skaman82/2.4GHz-Fatshark-Module/Documents/RX228D -90db VID only - not compatible/RX2288D.jpg

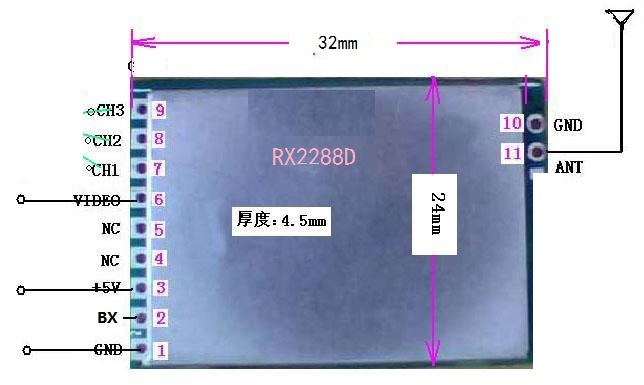
Documents/RX228D -90db VID only - not compatible/RX2288D.jpg
