skaman82/2.4GHz-Fatshark-Module/Documents/RX2189 -90db EOL no rssi/HT1ilCaFG4XXXagOFbXH.jpg

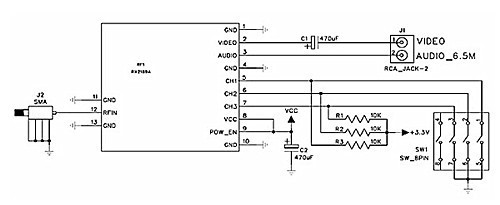
Documents/RX2189 -90db EOL no rssi/HT1ilCaFG4XXXagOFbXH.jpg
