skaman82/2.4GHz-Fatshark-Module/Documents/RX2189 -90db EOL no rssi/SKU075320.5.jpg

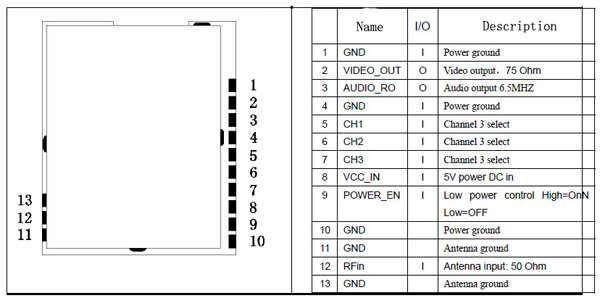
Documents/RX2189 -90db EOL no rssi/SKU075320.5.jpg
