skaman82/2.4GHz-Fatshark-Module/Documents/SM186R -90db no rssi/s-l1600-1.jpg

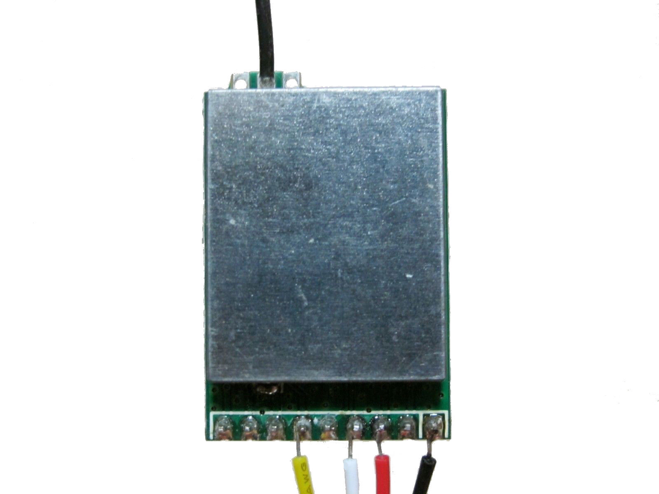
Documents/SM186R -90db no rssi/s-l1600-1.jpg
