skaman82/2.4GHz-Fatshark-Module/Documents/SM186R -90db no rssi/T2c0XlXnVNXXXXXXXX_!!104758930.jpg

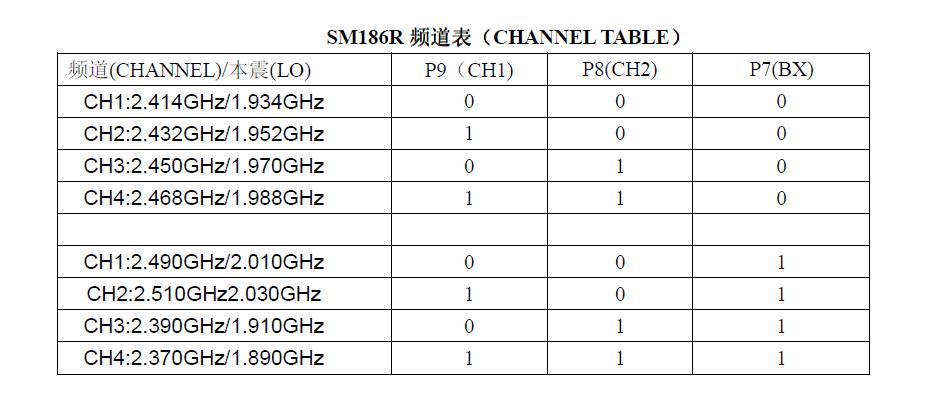
Documents/SM186R -90db no rssi/T2c0XlXnVNXXXXXXXX_!!104758930.jpg
