skaman82/2.4GHz-Fatshark-Module/pcb/module S-RX28_rev05 644_t.png

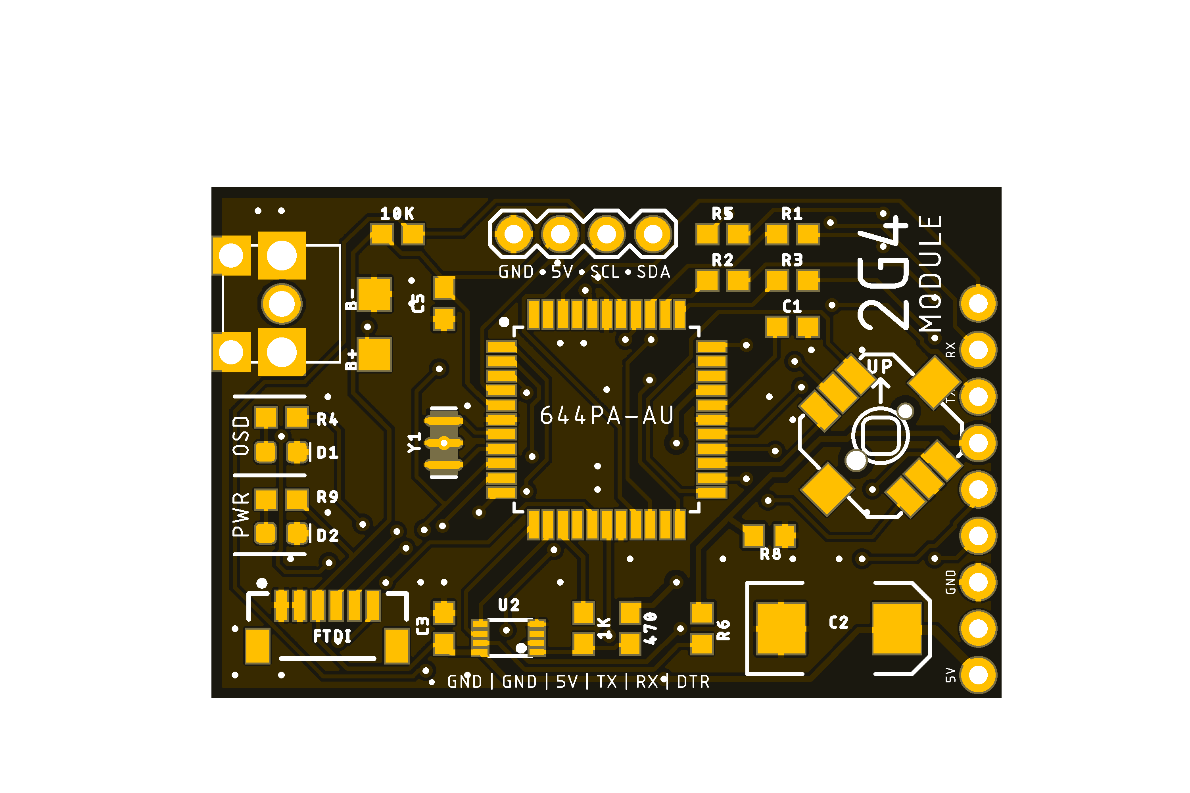
pcb/module S-RX28_rev05 644_t.png
