skaman82/2.4GHz-Fatshark-Module/Code/logo.h

#include <avr/pgmspace.h>
extern const unsigned char logo[];
extern const unsigned char bitmap_nkizw_OSD[];
extern const unsigned char bitmap_hd85pj_OSD[];
extern const unsigned char bitmap_w113l_OSD[];
extern const unsigned char bitmap_ydywrn_OSD[];
extern const unsigned char bitmap_949gqh_OSD[];
extern const unsigned char bitmap_be8bbq_OSD[];
extern const unsigned char bitmap_6zuzag_OSD[];
extern const unsigned char bitmap_display_OSD[];
extern const unsigned char bitmap_minilock_OSD[];
extern const unsigned char bitmap_minilockopen_OSD[];

extern const unsigned char bitmap_one_OSD[];
extern const unsigned char bitmap_two_OSD[];
extern const unsigned char bitmap_three_OSD[];
extern const unsigned char bitmap_four_OSD[];
extern const unsigned char bitmap_five_OSD[];
extern const unsigned char bitmap_six_OSD[];
extern const unsigned char bitmap_seven_OSD[];
extern const unsigned char bitmap_eight_OSD[];
